Karla012/design-current-meter/app_inventor/evidencias/BT_app.jpeg

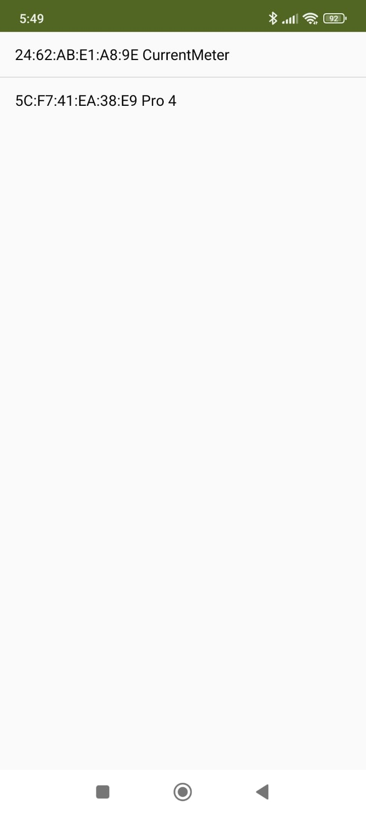
app_inventor/evidencias/BT_app.jpeg
