Karla012/design-current-meter/app_inventor/evidencias/main_app.jpeg

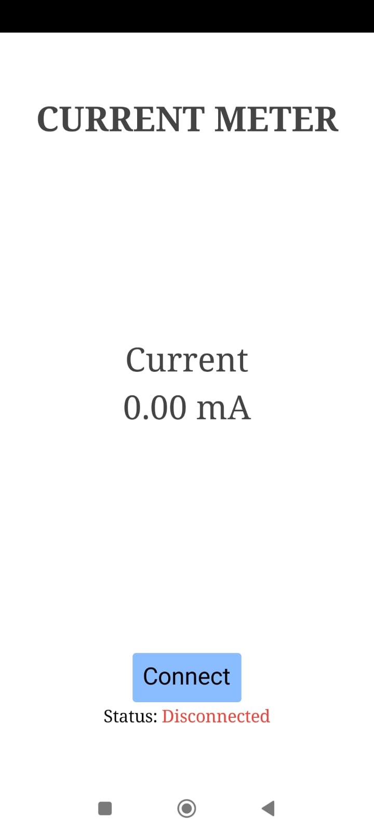
app_inventor/evidencias/main_app.jpeg
