Karla012/design-current-meter/hardware/esquematicos/E_amplificacion.png

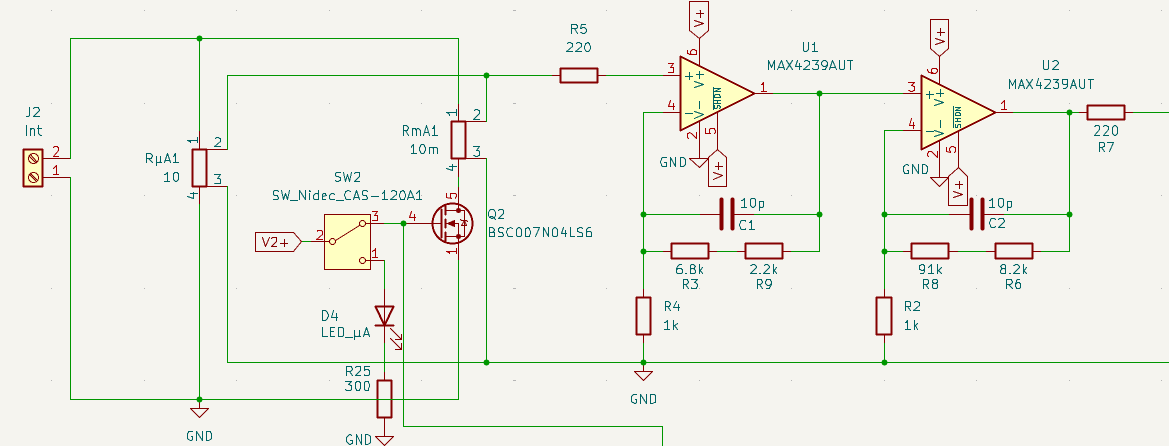
hardware/esquematicos/E_amplificacion.png
