Karla012/design-current-meter/simulacion/Monte0_01.png

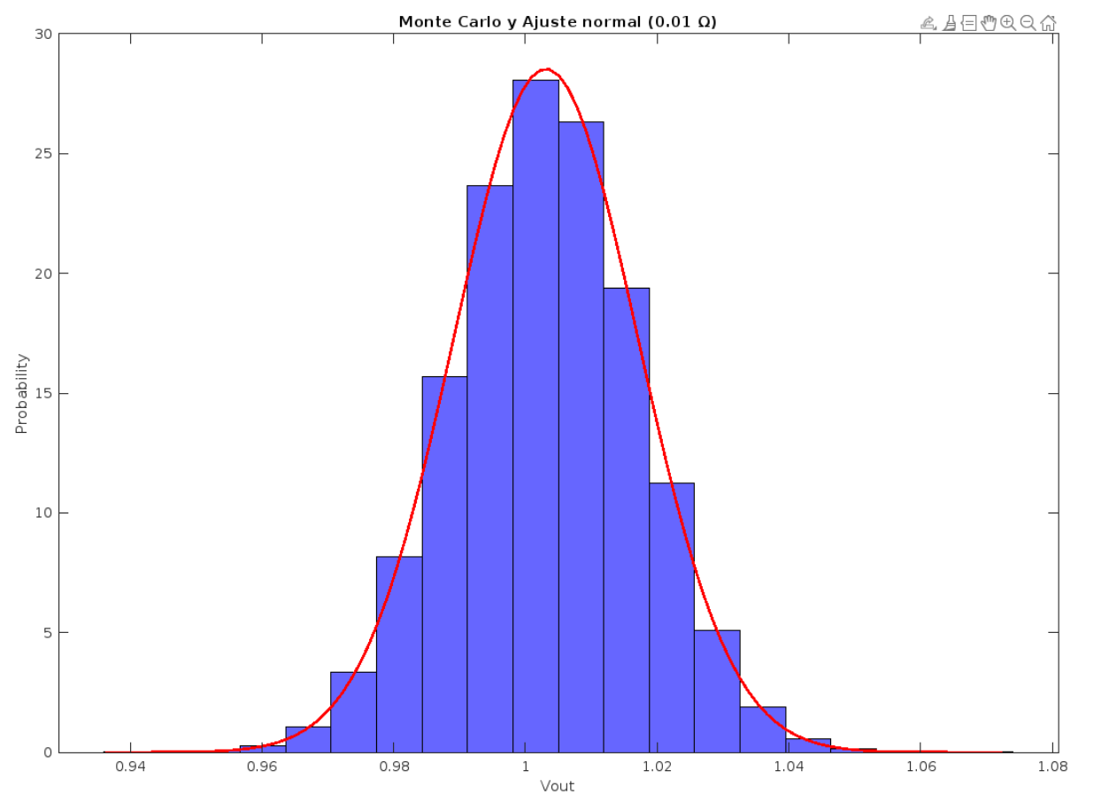
simulacion/Monte0_01.png
