Karla012/design-current-meter/simulacion/Montecarlo_0.01.png

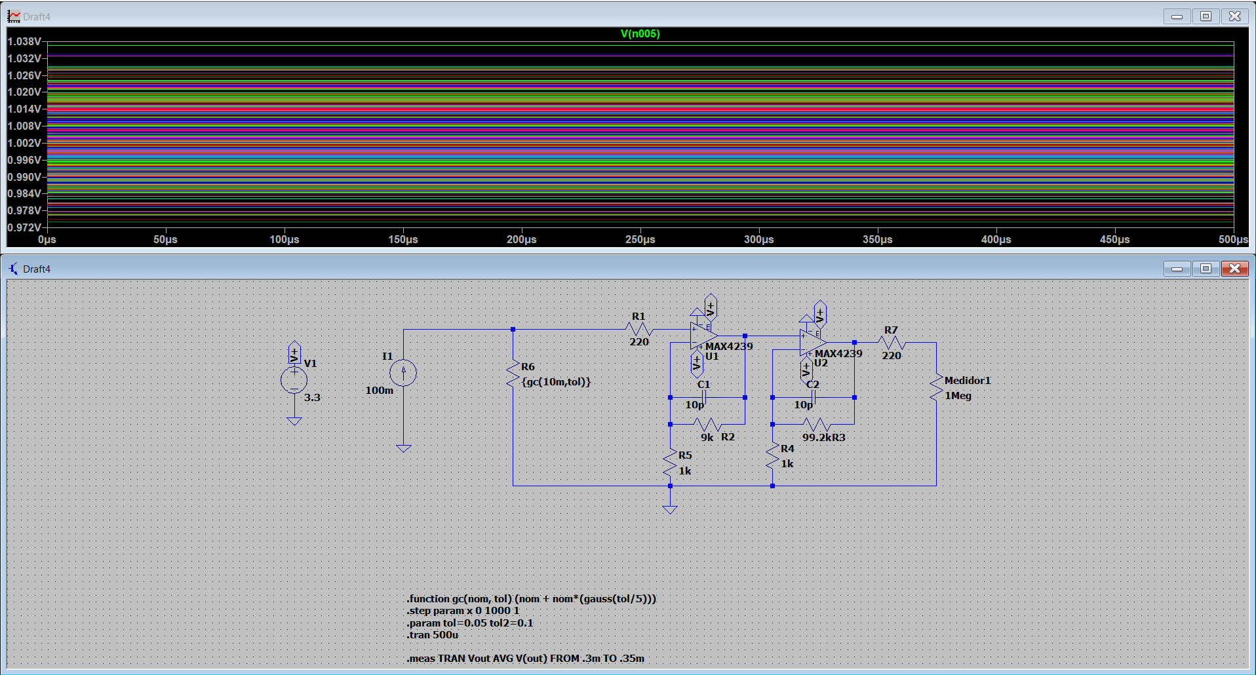
simulacion/Montecarlo_0.01.png
