Karla012/design-current-meter/simulacion/Montecarlo_10.png

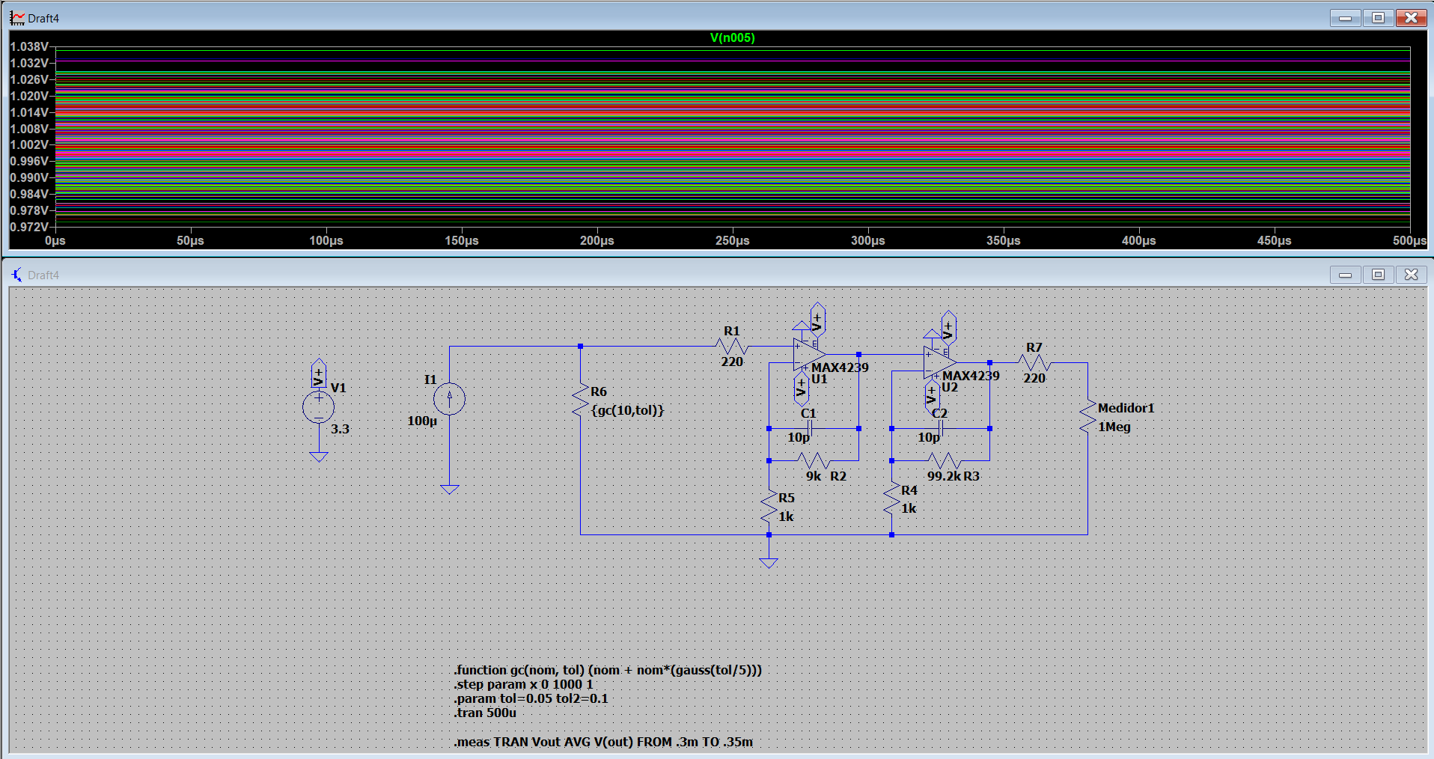
simulacion/Montecarlo_10.png
