Karla012/design-current-meter/simulacion/Muestras0_01.png

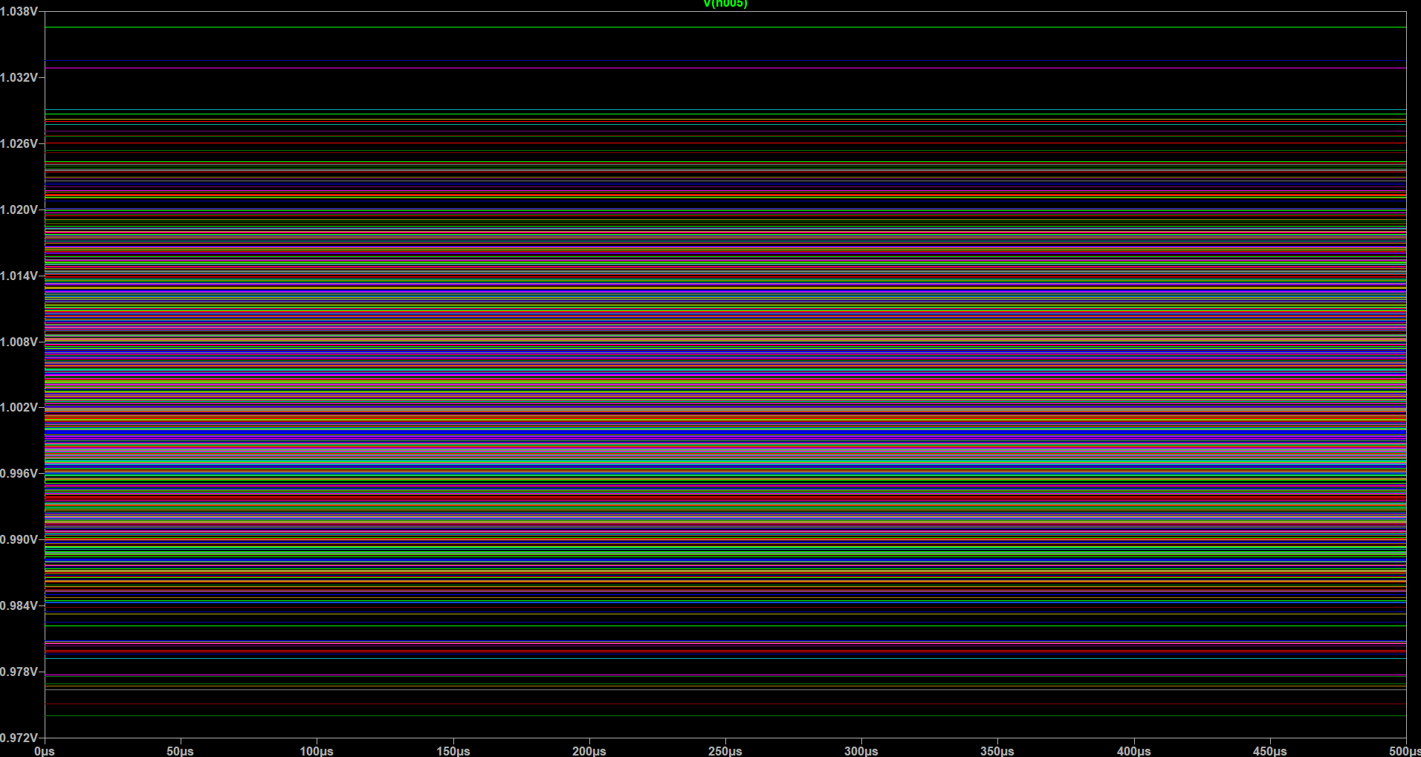
simulacion/Muestras0_01.png
