Karla012/design-current-meter/simulacion/Simulación_1.png

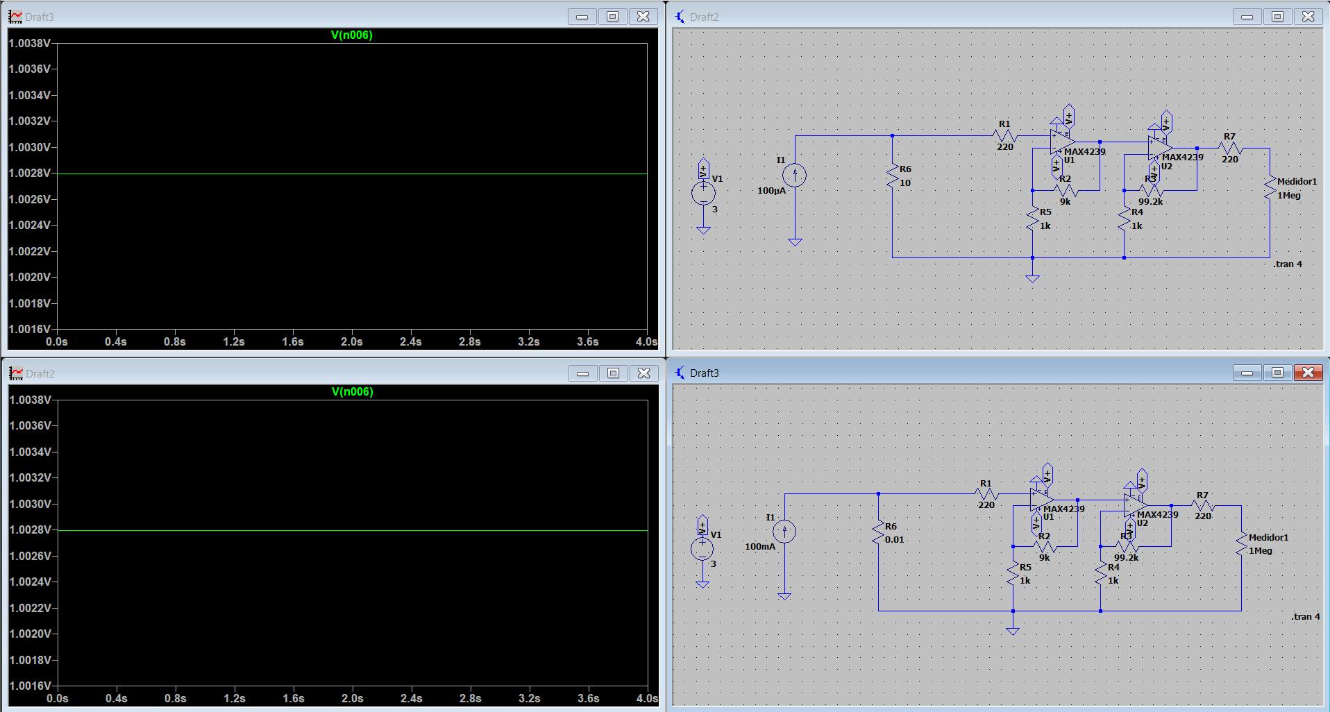
simulacion/Simulación_1.png
