Karla012/design-current-meter/simulacion/Draft3.asc

I1: current; 100mA
Medidor1: res; 100k
R1: res; 270
R2: res; 9k
R3: res; 99k
R4: res; 1k
R5: res; 1k
R6: res; 0.01
R7: res; 270
R8: res; 25k
R9: res; 5k
R10: res; 2k
R11: res; 1k
U1: MAX4239
U2: MAX4239
V1: voltage; 3
Named nets: 0, V+
.tran 4
