Karla012/design-current-meter/simulacion/Draft4.asc

C1: cap; 10p
C2: cap; 10p
I1: current; 100m
Medidor1: res; 1Meg
R1: res; 220
R2: res; 9k
R3: res; 99.2k
R4: res; 1k
R5: res; 1k
R6: res; {gc(10m,tol)}
R7: res; 220
U1: MAX4239
U2: MAX4239
V1: voltage; 3.3
Named nets: 0, V+
.function gc(nom, tol) (nom + nom*(gauss(tol/5)))
.step param x 0 1000 1
.param tol=0.05 tol2=0.1
.tran 500u
 
.meas TRAN Vout AVG V(out) FROM .3m TO .35m
