Karla012/design-current-meter/simulacion/Esquema_proyecto_Dis.asc

A1: inv
A2: and
A3: or
C1: cap; 10p
C2: cap; 10p
C3: cap; 10p
C4: cap; 10p
I1: current; 100µ
I2: current; 100m
Medidor: res; 1Meg
R1: res; 220
R2: res; 8.87k
R3: res; 100k
R4: res; 10k
R5: res; 1k
R6: res; 1k
R7: res; 10
R8: res; 220
R9: res; 5.1k
R10: res; 33k
R11: res; 5.1
R12: res; 10m
R13: res; 220
R14: res; 9k
R15: res; 1k
R16: res; 98k
R17: res; 1k
R18: res; 220
R19: res; 1Meg
U1: MAX4239
U2: MAX4239
U3: SN74AUP1G80; BUFFER_0
U4: IPT004N03L
U5: TLV3501
U6: MAX4239
U7: TLV3501
U8: MAX4239
V1: voltage; 3
Named nets: 0, V+
.tran 500u
Vmin
Vmax
0.46mV
1V
SN74AUP1G79
